gustavostuff/GameNerd/nano/apps/studio/app/src/ui/ui.h

#ifndef retr01_STUDIO_UI_H
#define retr01_STUDIO_UI_H

#include "retr01_studio/project.h"
#include "retr01_nano_emu/machine.h"
#include "r01_bgm_host.h"

#include <SDL.h>

#define UI_LOGIC_BASE_W 640
#define UI_LOGIC_BASE_H 360

/* Phase 2 chrome: dark / darker gray, 8px grid. */
#define UI_COL_BG_R 34
#define UI_COL_BG_G 34
#define UI_COL_BG_B 38
#define UI_COL_PANEL_R 26
#define UI_COL_PANEL_G 26
#define UI_COL_PANEL_B 30
#define UI_COL_WELL_R 63
#define UI_COL_WELL_G 63
#define UI_COL_WELL_B 74
#define UI_COL_ACTIVE_R 45
#define UI_COL_ACTIVE_G 125
#define UI_COL_ACTIVE_B 70
#define UI_COL_PRESENT_R 55
#define UI_COL_PRESENT_G 130
#define UI_COL_PRESENT_B 220
#define UI_COL_MARK_R 245
#define UI_COL_MARK_G 245
#define UI_COL_MARK_B 245
#define UI_COL_CHESS_A_R 58
#define UI_COL_CHESS_A_G 58
#define UI_COL_CHESS_A_B 66
#define UI_COL_CHESS_B_R 50
#define UI_COL_CHESS_B_G 50
#define UI_COL_CHESS_B_B 58

#define UI_UNIT 8
#define UI_BTN_H 16
#define UI_SIDEBAR_W 128
#define UI_CTRL_SIDEBAR_W 128
#define UI_WORLD_BTN 16
#define UI_WORLD_CELL 8 /* 16x16 map fits 128px sidebar */
#define UI_WORLD_VIEW 128
#define UI_PAL_SWATCH 8
#define UI_PAL_GRID_CELL 16 /* 4x4 picker cell (2x swatch) */
#define UI_PAL_GRID_SIZE (R01_PALS_PER_ROW * UI_PAL_GRID_CELL)
/* Nano FG picker: 2 rows × 4 colors (board FG 0..7). */
#define UI_FG_COLS 4
#define UI_FG_ROWS 2
#define UI_FG_CELL UI_PAL_GRID_CELL
#define UI_FG_GRID_W (UI_FG_COLS * UI_FG_CELL)
#define UI_FG_GRID_H (UI_FG_ROWS * UI_FG_CELL)

#define UI_WORLDS_X 0
#define UI_WORLDS_SUB_H 8
#define UI_TABS_TAB_H 8  /* active main tab height (16x16 inactive stack fill) */
#define UI_WORLDS_TAB_STACK_H 16 /* inactive dual-view tab fill / active main+sub */
#define UI_WORLDS_BODY_H (UI_BTN_H + UI_WORLD_VIEW)
#define UI_PAL_BODY_H (UI_PAL_SWATCH * 2 + UI_BTN_H)

#define UI_WORLDS_PLANE_BG1 0
#define UI_WORLDS_PLANE_BG0 1

#define UI_BANKS_PLANE_BG 0
#define UI_BANKS_N 4
#define UI_BANKS_GRID 128 /* 16x16 tiles @ 8px */
#define UI_BANKS_BODY_H (UI_BTN_H + UI_BANKS_GRID)

#define UI_ARM_NONE 0
#define UI_ARM_WORLD_TAB 1
#define UI_ARM_WORLD_SUB 2
#define UI_ARM_WORLD_CELL 3
#define UI_ARM_ACCORDION 4
#define UI_ARM_LAYER 5
#define UI_ARM_MODE 6
#define UI_ARM_PAL_STRIP 7
#define UI_ARM_PAL_ROW 8
#define UI_ARM_PLAY 9
#define UI_ARM_CATALOG_ADD 10
#define UI_ARM_BANK_TAB 12
#define UI_ARM_BANK_SUB 13
#define UI_ARM_APP_TAB 14
#define UI_ARM_SOUND_PLANE 15
#define UI_ARM_SOUND_TRACK 16
#define UI_ARM_SOUND_ADD 17
#define UI_ARM_SOUND_CH 18
#define UI_ARM_SOUND_PLAY 19
#define UI_ARM_SOUND_PAUSE 20
#define UI_ARM_SOUND_STOP 21

#define UI_APP_GRAPHICS 0
#define UI_APP_SOUNDS 1 /* Audio tab (historical enum name) */
#define UI_APP_CHROME_H UI_BTN_H /* Graphics|Audio strip, flush to content */

#define UI_SOUND_PLANE_BGM 0
#define UI_SOUND_PLANE_SFX 1
#define UI_SOUND_BGM_CH 1 /* Nano: single Music (Pulse) lane */
#define UI_SOUND_SOLO_ALL (-1) /* isolate radios: hear all channels */
#define UI_SOUND_SNAP_DIV R01_BGM_NOTE_DIV
#define UI_SOUND_STEPS_MAX R01_BGM_STEPS
#define UI_SOUND_TRACKS_MAX 8
#define UI_SOUND_REGIONS_MAX 128
#define UI_SOUND_CLIP_MAX 32
#define UI_SOUND_PX_PER_TICK 16 /* one 1/4-note tick = 2 grid cells */
#define UI_SOUND_LANE_H 16      /* channel strip height (2 grid cells) */
#define UI_SOUND_LANE_GAP 0
#define UI_SOUND_HANDLE_W 8
#define UI_SOUND_MINIMAP_H 8
#define UI_SOUND_SCROLL_PAD 4 /* unused for max; kept for content padding hints */

#define UI_SOUND_SEL_NONE 0
#define UI_SOUND_SEL_REGION 1
#define UI_SOUND_SEL_EMPTY 2

#define UI_SOUND_DRAG_NONE 0
#define UI_SOUND_DRAG_PAINT 1
#define UI_SOUND_DRAG_RESIZE_L 2
#define UI_SOUND_DRAG_RESIZE_R 3
#define UI_SOUND_DRAG_MOVE 4

#define UI_ACC_NONE (-1)
#define UI_ACC_WORLDS 0
#define UI_ACC_BANKS 1
#define UI_ACC_METATILES 2
/* When 1, all accordion sections stay expanded and headers do not collapse. */
#define UI_ACCORDION_ALWAYS_EXPANDED 0
#define UI_ACCORDION_ANIM_MS 250
#define UI_ACC_SECTIONS 3

#define UI_METATILES_BODY_H 96
#define UI_SPRITE_ROW_H 16
#define UI_PREVIEW_ICON 16

#define UI_DOT_SIZE 8
#define UI_DOT_GAP 0 /* packed strip, no gaps between dots */
#define UI_DOT_STRIP_N 4

/* Widget focus: wheel / keyboard route to the focused control. */
#define UI_FOCUS_NONE 0
#define UI_FOCUS_PALETTE 1
#define UI_FOCUS_WORKBENCH 2
#define UI_FOCUS_LIST 3

#define UI_MODE_ROW_H UI_BTN_H
#define UI_MODE_RADIO 8
#define UI_MODE_GAP 8
#define UI_CHECKBOX 8

#define UI_SCREEN_MODE_SEL 0
#define UI_SCREEN_MODE_PAINT 1

#define UI_SCREEN_LAYER_BG 0

#define UI_MODAL_W 288
#define UI_MODAL_H 184
#define UI_TILE_CANVAS 128
#define UI_MODAL_BODY_Y (UI_BTN_H + UI_UNIT)

#define UI_PAL_MODAL_W 320
#define UI_PAL_MODAL_H 192
#define UI_MASTER_COLS 16
#define UI_MASTER_ROWS 4
#define UI_MASTER_CELL 8
#define UI_PAL_EDIT_CELL UI_PAL_GRID_CELL

#define UI_TOAST_MS 2800
#define UI_TOOLTIP_DELAY_MS 400

#define UI_MENU_MAX 16
#define UI_MENU_KIND_TILE 1
#define UI_MENU_KIND_WORLD 2
#define UI_MENU_KIND_BANK_CELL 7
#define UI_MENU_KIND_METATILE 8
#define UI_MENU_SUB_NONE 0
#define UI_MENU_SUB_BANK 1
#define UI_MENU_SUB_PAL 2
#define UI_MENU_SUB_MOVE_BANK 6

typedef struct UiMenu {
    int open;
    int kind;
    int root_x, root_y;
    int root_w;
    int item_count;
    char items[UI_MENU_MAX][32];
    uint8_t item_sub[UI_MENU_MAX]; /* UI_MENU_SUB_* or 0 */
    uint8_t item_disabled[UI_MENU_MAX];

    int submenu;
    int sub_x, sub_y;
    int sub_w;
    int sub_count;
    char sub_items[UI_MENU_MAX][24];

    int screen_tx, screen_ty;
    int world_screen_idx;
    int metatile_idx;
    int bank_idx;     /* UI_MENU_KIND_BANK_CELL */
    int bank_tile_id;
    int bank_plane; /* UI_BANKS_PLANE_* */
} UiMenu;

typedef struct UiTileEdit {
    int open;
    int pal;   /* Nano FG color 0..7 */
    int color; /* paint ink 0/1 (1bpp) */
    int tile_id;
    int bank;
    int flip_h;
    int flip_v;
    int is_new;
    int edit_all; /* Shift: apply save to all matching tile+attr cells in world */
    uint8_t match_tile_id;
    uint8_t match_attr_hw; /* bank/pal/flips at open (R01_ATTR_HW_MASK) */
    uint8_t chr[R01_TILE_BYTES];
    int paint_tx, paint_ty; /* screen tile that opened the editor (-1 if none) */
} UiTileEdit;

typedef struct UiPalEdit {
    int open;
    int row;   /* 0..7 global palette row (BG + SPR) */
    int plane; /* 0 = BG, 1 = SPR */
    int pal;   /* 0..3 */
    int color; /* 0..3 */
    int snap_valid;
    int snap_default_row;
    R01PalRow snap_bg[R01_PAL_ROWS][R01_PALS_PER_ROW];
    R01PalRow snap_spr[R01_PAL_ROWS][R01_PALS_PER_ROW];
} UiPalEdit;

typedef struct UiBrush {
    int armed; /* after Save in tile editor */
    int bank;
    int tile_id;
    int pal; /* Nano: FG color 0..7 (attr bits) */
    int flip_h;
    int flip_v;
    uint8_t chr[R01_TILE_BYTES];
} UiBrush;

/* Painted note strip on a channel lane (UI source of truth; flattened for host). */
typedef struct UiBgmRegion {
    int start;   /* ticks */
    int len;     /* ticks, >= 1 */
    int midi;    /* melodic MIDI; noise period 0..15; DPCM kind stub */
    char tok[5]; /* host token */
} UiBgmRegion;

/* UI BGM shell (persisted in project.bgm). */
typedef struct UiSoundEdit {
    int plane; /* UI_SOUND_PLANE_BGM or SFX */
    int track_idx;
    int track_count;
    char track_name[UI_SOUND_TRACKS_MAX][24];
    int solo_ch; /* UI_SOUND_SOLO_ALL, or 0..UI_SOUND_BGM_CH-1 to isolate */
    int scroll_x; /* first visible tick */
    int sel_kind; /* UI_SOUND_SEL_* */
    int sel_ch;
    int sel_region; /* index when SEL_REGION */
    int sel_tick;   /* empty pivot tick when SEL_EMPTY */
    int playing;    /* host advancing */
    int paused;     /* halted but playhead retained */
    float play_pos; /* fractional tick; -1 idle */
    int drag;       /* UI_SOUND_DRAG_* */
    int drag_ch;
    int drag_region;
    int drag_origin;
    int drag_start0;
    int drag_len0;
    int drag_mx0; /* mouse x at paint/resize down (click vs drag) */
    int clip_valid;
    int clip_ch;
    int clip_count;
    UiBgmRegion clip[UI_SOUND_CLIP_MAX];
    int region_count[UI_SOUND_TRACKS_MAX][UI_SOUND_BGM_CH];
    UiBgmRegion region[UI_SOUND_TRACKS_MAX][UI_SOUND_BGM_CH][UI_SOUND_REGIONS_MAX];
} UiSoundEdit;

/* Single active text field (web-like caret / selection / scroll). */
typedef struct UiTextEdit {
    char *buf;
    int cap;
    int field_id; /* 0 = none; modal-specific otherwise */
    int caret;
    int anchor; /* selection other end; equals caret when collapsed */
    int scroll; /* horizontal px */
    int drag;   /* mouse-drag selecting */
} UiTextEdit;

/* Embedded emu Play session (export then cart-backed MAP preview). */
typedef struct UiPlaySession {
    int active;  /* playing or booting (blocks editor) */
    int booting; /* export + machine init pending after first boot frame */
    int spin;
    Uint32 last_tick;
    R01neMachine *machine;
    SDL_Texture *fb_tex;
    char err[256];
} UiPlaySession;

typedef struct UiState {
    R01Project *project;
    UiPlaySession play;
    char project_path[R01_PATH_MAX];
    char toast[96];
    Uint32 toast_until;
    int toast_error;
    char tooltip[160];
    int tooltip_x;
    int tooltip_y;
    int tooltip_arm_x; /* hover arm point; any move clears + resets delay */
    int tooltip_arm_y;
    int tooltip_active;
    int tooltip_hit; /* armed this frame via ui_tooltip_hover */
    Uint32 tooltip_since_ms;
    char tooltip_key[160];
    int scale;
    int logic_scale; /* 1 = 640x360, 2 = 1280x720 */
    Uint8 keys[512];
    int mouse_x;
    int mouse_y;
    UiMenu menu;
    UiTileEdit tile_edit;
    UiPalEdit pal_edit;
    UiTextEdit text;
    UiBrush brush;
    UiSoundEdit sound;
    int app_mode; /* UI_APP_GRAPHICS or UI_APP_SOUNDS */
    int paint_stamp_valid;
    uint8_t paint_stamp_tile;
    uint8_t paint_stamp_attr;
    int screen_mode;  /* UI_SCREEN_MODE_SEL or UI_SCREEN_MODE_PAINT */
    int screen_layer; /* UI_SCREEN_LAYER_BG */
    int sel_x0, sel_y0, sel_x1, sel_y1; /* inclusive tile rect; invalid when sel_x0 < 0 */
    int sel_anchor_x, sel_anchor_y;
    int sel_drag;
    int last_paint_tx;
    int last_paint_ty;
    Uint32 last_click_ms;
    int last_click_col;
    int last_click_row;
    int worlds_plane; /* UI_WORLDS_PLANE_BG1 or BG0 */
    int banks_idx;    /* 0..3 CHR bank tab */
    int banks_plane;  /* UI_BANKS_PLANE_BG */
    int world_sel_col; /* grid selection (-1 none); empty slots allowed */
    int world_sel_row;
    int screen_clip_valid;
    R01Screen screen_clip; /* Ctrl+C / Ctrl+V whole-screen buffer */
    int arm_kind;     /* UI_ARM_* chrome press-arm for release commit */
    int arm_a;
    int arm_b;
    int accordion_open; /* UI_ACC_* or UI_ACC_NONE */
    int accordion_body_h[UI_ACC_SECTIONS]; /* animated body height per section */
    Uint32 accordion_anim_last_ms;
    int metatiles_scroll;
    int focus; /* UI_FOCUS_* — which control owns wheel / key routing */
} UiState;

static inline int ui_logic_scale(const UiState *ui) {
    int s = ui ? ui->logic_scale : 2;
    return (s == 1) ? 1 : 2;
}

static inline int ui_logic_w(const UiState *ui) {
    return UI_LOGIC_BASE_W * ui_logic_scale(ui);
}

static inline int ui_logic_h(const UiState *ui) {
    return UI_LOGIC_BASE_H * ui_logic_scale(ui);
}

static inline int ui_main_w(const UiState *ui) {
    return ui_logic_w(ui) - UI_SIDEBAR_W - UI_CTRL_SIDEBAR_W;
}

static inline int ui_ctrl_x(const UiState *ui) {
    return ui_logic_w(ui) - UI_CTRL_SIDEBAR_W;
}

/*
 * Integer pixel scale for the 128×96 compose buffer in the main pane.
 * Largest fit between the sidebars, minus one (breathing room).
 */
static inline int ui_screen_scale(const UiState *ui) {
    int avail_w = ui_main_w(ui);
    int avail_h = ui_logic_h(ui) - UI_APP_CHROME_H - 2 * UI_UNIT;
    int max_sx;
    int max_sy;
    int s;
    (void)ui;
    if (avail_w < 1) {
        avail_w = 1;
    }
    if (avail_h < 1) {
        avail_h = 1;
    }
    max_sx = avail_w / R01_SCREEN_PX_W;
    max_sy = avail_h / R01_SCREEN_PX_H;
    s = max_sx < max_sy ? max_sx : max_sy;
    if (s > 1) {
        s -= 1;
    }
    if (s < 1) {
        s = 1;
    }
    return s;
}

static inline int ui_screen_w(const UiState *ui) {
    return R01_SCREEN_PX_W * ui_screen_scale(ui);
}

static inline int ui_screen_h(const UiState *ui) {
    return R01_SCREEN_PX_H * ui_screen_scale(ui);
}

static inline int ui_preview_x(const UiState *ui) {
    int pane = ui_main_w(ui);
    int sw = ui_screen_w(ui);
    int x = UI_SIDEBAR_W + (pane - sw) / 2;
    if (x < UI_SIDEBAR_W) {
        x = UI_SIDEBAR_W;
    }
    if (x + sw > ui_ctrl_x(ui)) {
        x = ui_ctrl_x(ui) - sw;
        if (x < UI_SIDEBAR_W) {
            x = UI_SIDEBAR_W;
        }
    }
    return x;
}

int ui_init(UiState *ui);
void ui_shutdown(UiState *ui);
void ui_tick(UiState *ui);
void ui_draw(UiState *ui, SDL_Renderer *r);
void ui_toggle_logic_scale(UiState *ui);
int ui_handle_event(UiState *ui, const SDL_Event *e, int lx, int ly);
int ui_handle_drop_file(UiState *ui, const char *path, int lx, int ly);

#endif
