gustavostuff/GameNerd/nano/apps/studio/app/src/ui/internal.h

#ifndef retr01_STUDIO_UI_INTERNAL_H
#define retr01_STUDIO_UI_INTERNAL_H

#include "ui/ui.h"
#include "ui/widgets/widgets.h"

#include <SDL.h>
#include <stdint.h>

typedef struct UiClipStack {
    SDL_Rect prev;
    SDL_bool had_clip;
} UiClipStack;

typedef struct AccordionLayout {
    int worlds_hdr_y;
    int worlds_btns_y;
    int worlds_grid_y;
    int worlds_open;
    int worlds_body_h;
    int banks_hdr_y;
    int banks_body_y;
    int banks_open;
    int banks_body_h;
    int metatiles_hdr_y;
    int metatiles_body_y;
    int metatiles_open;
    int metatiles_body_h;
} AccordionLayout;

typedef struct SoundEditorLayout {
    int content_y;
    int plane_tabs_x, plane_tabs_y, plane_tab_w;
    int track_list_y, track_row_h;
    int add_x, add_y, add_w;
    int hdr_y;
    int lane_label_x, lane_label_w;
    int timeline_x, timeline_y, timeline_w, timeline_h;
    int lane_h, lane_gap;
    int px_per_tick;
    int visible_ticks;
    int ruler_h;
    int minimap_y, minimap_h;
    int insp_x, insp_y;
    int play_x, play_y, play_w;
    int pause_x, pause_y, pause_w;
    int stop_x, stop_y, stop_w;
    int ch_radio_y0;
} SoundEditorLayout;

static inline void ui_world_btn_pos(int wi, int btns_y, int *out_x, int *out_y) {
    if (out_x) {
        *out_x = UI_WORLDS_X + wi * UI_WORLD_BTN;
    }
    if (out_y) {
        *out_y = btns_y;
    }
}

typedef struct TileModalLayout {
    int mx, my;
    int pal_x, pal_label_y, pal_y;
    int canvas_x, canvas_y;
    int btn_y, save_w, cancel_w;
} TileModalLayout;

typedef struct PalModalLayout {
    int mx, my;
    int master_x, master_y;
    int bg_label_y, bg_x, bg_y;
    int spr_label_y, spr_x, spr_y;
    int btn_y, save_w, cancel_w;
} PalModalLayout;

extern uint8_t *g_radio_rgba;
extern int g_radio_w;
extern int g_radio_h;
extern uint8_t *g_dot_rgba;
extern int g_dot_w;
extern int g_dot_h;
extern uint8_t *g_checkbox_rgba;
extern int g_checkbox_w;
extern int g_checkbox_h;
extern uint8_t *g_cross_rgba;
extern int g_cross_w;
extern int g_cross_h;
extern uint8_t *g_bg0_btn_rgba;
extern int g_bg0_btn_w;
extern int g_bg0_btn_h;
extern uint8_t *g_bg1_btn_rgba;
extern int g_bg1_btn_w;
extern int g_bg1_btn_h;
extern uint8_t *g_bg_bank_btn_rgba;
extern int g_bg_bank_btn_w;
extern int g_bg_bank_btn_h;
extern uint8_t *g_spr_bank_btn_rgba;
extern int g_spr_bank_btn_w;
extern int g_spr_bank_btn_h;

extern SDL_Cursor *g_cursor_arrow;
extern SDL_Cursor *g_cursor_hand;
extern SDL_Cursor *g_cursor_sizewe;

int ui_load_png_rgba(const char *path, uint8_t **out_px, int *out_w, int *out_h);
int ui_paste_clipboard_png_tile(UiState *ui, uint8_t chr[R01_TILE_BYTES], int pal, int spr_plane);
int snap8(int v);
void ui_toast(UiState *ui, const char *msg, int is_error);
void ui_tooltip_set(UiState *ui, int x, int y, const char *line1, const char *line2);
void ui_tooltip_hover(UiState *ui, int x, int y, const char *line1, const char *line2);
void ui_tooltip_frame_begin(UiState *ui);
void ui_tooltip_frame_end(UiState *ui);
void ui_tooltip_clear(UiState *ui);
void draw_tooltip(UiState *ui, SDL_Renderer *r);
void ui_focus_set(UiState *ui, int focus);
int ui_focus_get(const UiState *ui);
void ui_focus_clear(UiState *ui);
void fill_rect(SDL_Renderer *r, int x, int y, int w, int h, Uint8 R, Uint8 G, Uint8 B);
void fill_rect_alpha(SDL_Renderer *r, int x, int y, int w, int h, Uint8 R, Uint8 G, Uint8 B, Uint8 A);
void ui_clip_push(SDL_Renderer *r, int x, int y, int w, int h, UiClipStack *stack);
void ui_clip_pop(SDL_Renderer *r, const UiClipStack *stack);
void draw_rect(SDL_Renderer *r, int x, int y, int w, int h, Uint8 R, Uint8 G, Uint8 B);
void hover_overlay(SDL_Renderer *r, int x, int y, int w, int h);
void font_draw_clipped(SDL_Renderer *r, int x, int y, int clip_x, int clip_y, int clip_w, int clip_h,
                       const char *text, Uint8 R, Uint8 G, Uint8 B);
int point_in_rect(int lx, int ly, int x, int y, int w, int h);
int label_width(const char *text);
void draw_brush_preview(SDL_Renderer *r, const R01Project *p, int row, int pal, int color, int mx, int my);
void draw_ui_cross(SDL_Renderer *r, int cx, int cy);
void draw_label(SDL_Renderer *r, int x, int y, const char *text);
void draw_chess_grid(SDL_Renderer *r, int x0, int y0, int cols, int rows, int cell);

void ui_editor_layout(const UiState *ui, int *screen_x, int *screen_y, int *layer_x, int *mode_x, int *mode_y0);
void ui_preview_size(const UiState *ui, int *out_w, int *out_h);
int screen_mode_hit(const UiState *ui, int lx, int ly, int *out_row);
int screen_mode_row_hit(const UiState *ui, int lx, int ly, int row);
int screen_layer_hit(const UiState *ui, int lx, int ly, int *out_layer);
int screen_layer_row_hit(const UiState *ui, int lx, int ly, int row);
int ui_mode_label_x(int mode_x);
int ui_mode_panel_w(void);
int ui_layer_panel_w(void);
void screen_origin(const UiState *ui, int *ox, int *oy);
int screen_hit(const UiState *ui, int lx, int ly, int *out_tx, int *out_ty);
int screen_pixel_hit(const UiState *ui, int lx, int ly, int *out_px, int *out_py);
void accordion_init_heights(UiState *ui);
void accordion_anim_tick(UiState *ui);
void accordion_layout(const UiState *ui, AccordionLayout *lo);
int world_cell_hit(const UiState *ui, int lx, int ly, int *out_col, int *out_row);
int world_btn_hit(const UiState *ui, int lx, int ly, int *out_wi);
int world_sub_hit(const UiState *ui, int lx, int ly);
void worlds_tabs_prepare(const UiState *ui, UiTabsLayout *out);
int accordion_header_hit(const UiState *ui, int lx, int ly, int *out_section);
void accordion_toggle(UiState *ui, int section);
void draw_accordion_header(SDL_Renderer *r, int y, const char *title, int open, int hover);
void app_mode_tabs_prepare(const UiState *ui, UiTabsLayout *out);
int app_mode_tab_hit(const UiState *ui, int lx, int ly, int *out_idx);
void draw_app_mode_tabs(UiState *ui, SDL_Renderer *r);
void sound_editor_layout(const UiState *ui, SoundEditorLayout *lo);
void sound_plane_tabs_prepare(const UiState *ui, UiTabsLayout *out);
int sound_plane_tab_hit(const UiState *ui, int lx, int ly, int *out_idx);
int sound_track_hit(const UiState *ui, int lx, int ly, int *out_idx);
int sound_add_hit(const UiState *ui, int lx, int ly);
int sound_timeline_hit(const UiState *ui, int lx, int ly, int *out_ch, int *out_tick);
int sound_region_hit(const UiState *ui, int lx, int ly, int *out_ch, int *out_region, int *out_handle);
int sound_channel_hit(const UiState *ui, int lx, int ly, int *out_ch);
int sound_play_hit(const UiState *ui, int lx, int ly);
int sound_pause_hit(const UiState *ui, int lx, int ly);
int sound_stop_hit(const UiState *ui, int lx, int ly);
void ui_sound_init(UiState *ui);
int ui_sound_audio_init(void);
void ui_sound_audio_shutdown(void);
void ui_sound_play_start(UiState *ui);
void ui_sound_play_stop(UiState *ui);
void ui_sound_play_pause(UiState *ui);
void ui_sound_play_toggle(UiState *ui);
void ui_sound_play_poll(UiState *ui);
int ui_sound_play_step(void);
void tile_modal_layout(const UiState *ui, TileModalLayout *lo);
void pal_modal_layout(const UiState *ui, PalModalLayout *lo);
int play_btn_w(const UiState *ui);
int play_btn_x(const UiState *ui);
int play_btn_y(const UiState *ui);
int play_button_hit(const UiState *ui, int lx, int ly);
int banks_cell_hit(const UiState *ui, int lx, int ly, int *out_tile_id);
int banks_tab_hit(const UiState *ui, int lx, int ly, int *out_idx);
int banks_sub_hit(const UiState *ui, int lx, int ly);
void banks_tabs_prepare(const UiState *ui, UiTabsLayout *out);
int metatiles_list_hit(const UiState *ui, int lx, int ly, int *out_idx);
int metatiles_add_hit(const UiState *ui, int lx, int ly);

int palette_strip_hit(const UiState *ui, int lx, int ly);
int palette_row_btn_hit(const UiState *ui, int lx, int ly, int *out_row);
void pal_edit_close(UiState *ui);
void pal_edit_cancel(UiState *ui);
void pal_edit_save(UiState *ui);
void pal_edit_open(UiState *ui);
void pal_edit_set_row(UiState *ui, int row, int commit_default);
void pal_edit_nudge_master(UiState *ui, int wheel_y, int shift);
int pal_modal_master_hit(const UiState *ui, int lx, int ly, int *out_col, int *out_row);
int pal_modal_plane_hit(const UiState *ui, int lx, int ly, int plane, int *out_pal, int *out_color);
int pal_modal_handle(UiState *ui, int lx, int ly, int down);
void draw_pal_modal(UiState *ui, SDL_Renderer *r);

void menu_close(UiState *ui);
void menu_sync_tile_edit_label(UiState *ui);
void menu_open_tile(UiState *ui, int x, int y, int tx, int ty);
void menu_open_world_cell(UiState *ui, int x, int y, int screen_idx);
void menu_open_bank_cell(UiState *ui, int x, int y, int bank, int tile_id, int plane);
void menu_open_metatile(UiState *ui, int x, int y, int metatile_idx);
int menu_hit(const UiState *ui, int lx, int ly, int *out_item, int *out_sub);
void menu_update_hover(UiState *ui, int lx, int ly);
void handle_menu_pick(UiState *ui, int item, int is_sub);

void screen_sel_set(UiState *ui, int x0, int y0, int x1, int y1);
void screen_sel_clear(UiState *ui);
int screen_sel_valid(const UiState *ui);
void screen_sel_bounds(const UiState *ui, int *min_x, int *min_y, int *max_x, int *max_y);
void screen_refresh_sel(UiState *ui);
int screen_sel_is_multi(const UiState *ui);

void ui_paint_stamp_set(UiState *ui, uint8_t tile, uint8_t attr);
void ui_paint_stamp_from_bank(UiState *ui, int bank, int tile_id);
void ui_paint_stamp_from_cell(UiState *ui, int tx, int ty);
int ui_paint_stamp_from_sel(const UiState *ui, uint8_t *out_tile, uint8_t *out_attr);
void ui_paint_tile(UiState *ui, int tx, int ty);
void ui_flood_fill(UiState *ui, int tx, int ty);

void ui_toggle_play(UiState *ui);
void ui_play_stop(UiState *ui);
void ui_play_boot_finish(UiState *ui, SDL_Renderer *ren);
int ui_play_screen_mark(const UiState *ui);
void screen_set_sel_bank(UiState *ui, int bank);
void screen_set_sel_pal(UiState *ui, int pal);
void screen_toggle_sel_flag(UiState *ui, uint8_t flag);
void screen_set_solid_by_hw(UiState *ui, int ref_tx, int ref_ty);

void draw_screen_editor(UiState *ui, SDL_Renderer *r, const R01Screen *s);
void draw_play_view(UiState *ui, SDL_Renderer *r);
void draw_catalog_drag_ghost(UiState *ui, SDL_Renderer *r);

void tile_edit_open(UiState *ui, int tx, int ty);
void tile_edit_open_all(UiState *ui, int tx, int ty);
void tile_edit_open_new(UiState *ui, int tx, int ty);
void tile_edit_open_bank(UiState *ui, int bank, int tile_id, int is_new);
int tile_modal_handle(UiState *ui, int lx, int ly, int down, Uint8 button);
void draw_tile_modal(UiState *ui, SDL_Renderer *r);

void ui_update_cursor(const UiState *ui);
void draw_screen_mode(UiState *ui, SDL_Renderer *r);
void draw_ctrl_sidebar(UiState *ui, SDL_Renderer *r);
void draw_sound_editor(UiState *ui, SDL_Renderer *r);
void draw_sidebar(UiState *ui, SDL_Renderer *r);
void draw_menu(UiState *ui, SDL_Renderer *r);

void ui_reset_after_project_load(UiState *ui);
void ui_save(UiState *ui);
void ui_export(UiState *ui);

int ui_screen_nav(UiState *ui, int dcol, int drow);
R01Screen *ui_edit_map_screen(const UiState *ui);
void handle_world_click(UiState *ui, int col, int row, int ctrl, int dbl);
int ui_world_screen_copy(UiState *ui);
int ui_world_screen_paste(UiState *ui);
int ui_world_screen_remove(UiState *ui);

#endif
