gustavostuff/GameNerd/nano/apps/studio/app/src/ui/layout.c

#include "ui/ui.h"
#include "ui/internal.h"
#include "ui/sound/bgm_edit.h"
#include "font/font.h"

#include "retr01_studio/cart.h"
#include "retr01_studio/chr_pack.h"
#include "retr01_studio/json_io.h"
#include "retr01_studio/palette.h"
#include "retr01_studio/project.h"

#include <png.h>
#include <stdio.h>
#include <stdlib.h>
#include <string.h>

int ui_mode_panel_w(void) {
    int label_x = UI_MODE_RADIO + UI_MODE_GAP;
    int w0 = label_x + label_width("Tile selection");
    int w1 = label_x + label_width("Tile paint");
    int w = w0;
    if (w1 > w) {
        w = w1;
    }
    return w;
}

int ui_layer_panel_w(void) {
    return ui_mode_panel_w();
}

void ui_preview_size(const UiState *ui, int *out_w, int *out_h) {
    if (out_w) {
        *out_w = ui_screen_w(ui);
    }
    if (out_h) {
        *out_h = ui_screen_h(ui);
    }
}

void ui_editor_layout(const UiState *ui, int *screen_x, int *screen_y, int *layer_x, int *mode_x, int *mode_y0) {
    int sx = ui_preview_x(ui);
    int sy;
    int sh = ui_screen_h(ui);
    int chrome = UI_APP_CHROME_H;
    int content_h;
    int ctrl_inner = ui_ctrl_x(ui) + UI_UNIT;
    int radios_y = chrome + UI_BTN_H + UI_UNIT;
    int y_max;

    content_h = ui_logic_h(ui) - chrome;
    sy = chrome + (content_h - sh) / 2;
    if (sy < chrome + UI_UNIT) {
        sy = chrome + UI_UNIT;
    }
    y_max = ui_logic_h(ui) - UI_UNIT - sh;
    if (y_max < chrome + UI_UNIT) {
        y_max = chrome + UI_UNIT;
    }
    if (sy > y_max) {
        sy = y_max;
    }
    if (screen_x) {
        *screen_x = sx;
    }
    if (screen_y) {
        *screen_y = sy;
    }
    if (layer_x) {
        *layer_x = ctrl_inner;
    }
    if (mode_x) {
        *mode_x = ctrl_inner;
    }
    if (mode_y0) {
        *mode_y0 = radios_y;
    }
}

int ui_mode_label_x(int mode_x) {
    return mode_x + UI_MODE_RADIO + UI_MODE_GAP;
}

int screen_mode_row_hit(const UiState *ui, int lx, int ly, int row) {
    int sx, sy, layer_x, mx, my0;
    int y;
    if (!ui || ui->play.active) {
        return 0;
    }
    ui_editor_layout(ui, &sx, &sy, &layer_x, &mx, &my0);
    /* Mode radios: rows 0 and 1 (Tile selection / Tile paint). */
    y = my0 + row * UI_MODE_ROW_H;
    return point_in_rect(lx, ly, mx, y, ui_mode_panel_w(), UI_MODE_ROW_H);
}

int screen_mode_hit(const UiState *ui, int lx, int ly, int *out_row) {
    if (screen_mode_row_hit(ui, lx, ly, 0)) {
        if (out_row) {
            *out_row = UI_SCREEN_MODE_SEL;
        }
        return 1;
    }
    if (screen_mode_row_hit(ui, lx, ly, 1)) {
        if (out_row) {
            *out_row = UI_SCREEN_MODE_PAINT;
        }
        return 1;
    }
    return 0;
}

int screen_layer_row_hit(const UiState *ui, int lx, int ly, int row) {
    (void)ui;
    (void)lx;
    (void)ly;
    (void)row;
    return 0;
}

int screen_layer_hit(const UiState *ui, int lx, int ly, int *out_layer) {
    (void)ui;
    (void)lx;
    (void)ly;
    if (out_layer) {
        *out_layer = UI_SCREEN_LAYER_BG;
    }
    return 0;
}

int play_btn_w(const UiState *ui) {
    return label_width(ui->play.active ? "Stop" : "Play");
}

int play_btn_x(const UiState *ui) {
    int w = play_btn_w(ui);
    (void)ui;
    return ui_ctrl_x(ui) + (UI_CTRL_SIDEBAR_W - w) / 2;
}

int play_btn_y(const UiState *ui) {
    (void)ui;
    return UI_APP_CHROME_H;
}

int play_button_hit(const UiState *ui, int lx, int ly) {
    int x = play_btn_x(ui);
    int y = play_btn_y(ui);
    int w = play_btn_w(ui);
    return lx >= x && lx < x + w && ly >= y && ly < y + UI_BTN_H;
}

void screen_origin(const UiState *ui, int *ox, int *oy) {
    int sx, sy, layer_x, mx, my0;
    ui_editor_layout(ui, &sx, &sy, &layer_x, &mx, &my0);
    *ox = sx;
    *oy = sy;
}

int screen_hit(const UiState *ui, int lx, int ly, int *out_tx, int *out_ty) {
    int ox, oy;
    int lx0, ly0;
    screen_origin(ui, &ox, &oy);
    if (lx < ox || ly < oy || lx >= ox + ui_screen_w(ui) || ly >= oy + ui_screen_h(ui)) {
        return 0;
    }
    lx0 = (lx - ox) / ui_screen_scale(ui);
    ly0 = (ly - oy) / ui_screen_scale(ui);
    if (lx0 >= R01_SCREEN_PX_W || ly0 >= R01_SCREEN_PX_H) {
        return 0;
    }
    if (out_tx) {
        *out_tx = lx0 / 8;
    }
    if (out_ty) {
        *out_ty = ly0 / 8;
    }
    return 1;
}

int screen_pixel_hit(const UiState *ui, int lx, int ly, int *out_px, int *out_py) {
    int ox, oy;
    int px, py;
    screen_origin(ui, &ox, &oy);
    if (lx < ox || ly < oy || lx >= ox + ui_screen_w(ui) || ly >= oy + ui_screen_h(ui)) {
        return 0;
    }
    px = (lx - ox) / ui_screen_scale(ui);
    py = (ly - oy) / ui_screen_scale(ui);
    if (px < 0 || py < 0 || px >= R01_SCREEN_PX_W || py >= R01_SCREEN_PX_H) {
        return 0;
    }
    if (out_px) {
        *out_px = px;
    }
    if (out_py) {
        *out_py = py;
    }
    return 1;
}

void accordion_layout(const UiState *ui, AccordionLayout *lo) {
    int y = UI_APP_CHROME_H;
    int always = UI_ACCORDION_ALWAYS_EXPANDED;
    int worlds_h = 0;
    int banks_h = 0;
    int metatiles_h = 0;

    memset(lo, 0, sizeof(*lo));
    lo->metatiles_hdr_y = -1;
    lo->metatiles_body_y = -1;

    if (always) {
        worlds_h = UI_WORLDS_BODY_H;
        banks_h = UI_BANKS_BODY_H;
        metatiles_h = UI_METATILES_BODY_H;
    } else if (ui) {
        worlds_h = ui->accordion_body_h[UI_ACC_WORLDS];
        banks_h = ui->accordion_body_h[UI_ACC_BANKS];
        metatiles_h = ui->accordion_body_h[UI_ACC_METATILES];
    }

    lo->worlds_hdr_y = y;
    y += UI_BTN_H;
    lo->worlds_open = always || (ui && ui->accordion_open == UI_ACC_WORLDS);
    lo->worlds_body_h = worlds_h;
    if (worlds_h > 0) {
        lo->worlds_btns_y = y;
        lo->worlds_grid_y = y + UI_BTN_H;
        y += worlds_h;
    } else {
        lo->worlds_btns_y = -1;
        lo->worlds_grid_y = -1;
    }

    lo->banks_hdr_y = y;
    y += UI_BTN_H;
    lo->banks_open = always || (ui && ui->accordion_open == UI_ACC_BANKS);
    lo->banks_body_h = banks_h;
    if (banks_h > 0) {
        lo->banks_body_y = y;
        y += banks_h;
    } else {
        lo->banks_body_y = -1;
    }

    lo->metatiles_hdr_y = y;
    y += UI_BTN_H;
    lo->metatiles_open = always || (ui && ui->accordion_open == UI_ACC_METATILES);
    lo->metatiles_body_h = metatiles_h;
    if (metatiles_h > 0) {
        lo->metatiles_body_y = y;
        y += metatiles_h;
    } else {
        lo->metatiles_body_y = -1;
    }
}

static int accordion_section_full_h(int section) {
    switch (section) {
    case UI_ACC_WORLDS:
        return UI_WORLDS_BODY_H;
    case UI_ACC_BANKS:
        return UI_BANKS_BODY_H;
    case UI_ACC_METATILES:
        return UI_METATILES_BODY_H;
    default:
        return 0;
    }
}

void accordion_init_heights(UiState *ui) {
    int i;
    if (!ui) {
        return;
    }
    for (i = 0; i < UI_ACC_SECTIONS; i++) {
        int full = accordion_section_full_h(i);
        if (UI_ACCORDION_ALWAYS_EXPANDED || ui->accordion_open == i) {
            ui->accordion_body_h[i] = full;
        } else {
            ui->accordion_body_h[i] = 0;
        }
    }
    ui->accordion_anim_last_ms = SDL_GetTicks();
}

void accordion_anim_tick(UiState *ui) {
    Uint32 now;
    Uint32 dt;
    int i;

    if (!ui) {
        return;
    }
    now = SDL_GetTicks();
    dt = now - ui->accordion_anim_last_ms;
    ui->accordion_anim_last_ms = now;
    if (dt > 100u) {
        dt = 100u;
    }
    if (UI_ACCORDION_ALWAYS_EXPANDED) {
        for (i = 0; i < UI_ACC_SECTIONS; i++) {
            ui->accordion_body_h[i] = accordion_section_full_h(i);
        }
        return;
    }
    for (i = 0; i < UI_ACC_SECTIONS; i++) {
        int full = accordion_section_full_h(i);
        int target = (ui->accordion_open == i) ? full : 0;
        int cur = ui->accordion_body_h[i];
        int step;

        if (cur == target || full <= 0) {
            continue;
        }
        step = (int)((long long)full * (long long)dt / UI_ACCORDION_ANIM_MS);
        if (step < 1) {
            step = 1;
        }
        if (cur < target) {
            cur += step;
            if (cur > target) {
                cur = target;
            }
        } else {
            cur -= step;
            if (cur < target) {
                cur = target;
            }
        }
        ui->accordion_body_h[i] = cur;
    }
}
int world_cell_hit(const UiState *ui, int lx, int ly, int *out_col, int *out_row) {
    AccordionLayout lo;
    int x0 = UI_WORLDS_X;
    int y0;
    int col, row;
    accordion_layout(ui, &lo);
    if (lo.worlds_body_h < 1) {
        return 0;
    }
    y0 = lo.worlds_grid_y;
    if (lo.worlds_body_h <= UI_BTN_H || y0 < 0) {
        return 0;
    }
    if (lx < x0 || ly < y0 || lx >= x0 + R01_GRID_MAX * UI_WORLD_CELL ||
        ly >= y0 + R01_GRID_MAX * UI_WORLD_CELL) {
        return 0;
    }
    if (ly >= lo.worlds_btns_y + lo.worlds_body_h) {
        return 0;
    }
    col = (lx - x0) / UI_WORLD_CELL;
    row = (ly - y0) / UI_WORLD_CELL;
    if (col < 0 || row < 0 || col >= R01_GRID_MAX || row >= R01_GRID_MAX) {
        return 0;
    }
    if (out_col) {
        *out_col = col;
    }
    if (out_row) {
        *out_row = row;
    }
    return 1;
}

int world_btn_hit(const UiState *ui, int lx, int ly, int *out_wi) {
    AccordionLayout lo;
    UiTabsLayout tabs;
    int sel;
    accordion_layout(ui, &lo);
    if (lo.worlds_body_h < 1 || lo.worlds_btns_y < 0) {
        return 0;
    }
    worlds_tabs_prepare(ui, &tabs);
    sel = (ui && ui->project) ? ui->project->active_world : 0;
    return ui_tabs_hit(&tabs, sel, lx, ly, out_wi);
}

void worlds_tabs_prepare(const UiState *ui, UiTabsLayout *out) {
    AccordionLayout lo;
    static const char *const world_labs[R01_MAX_WORLDS] = {"", "", "", "", "", "", "", ""};
    if (!out) {
        return;
    }
    accordion_layout(ui, &lo);
    ui_tabs_layout(world_labs, R01_MAX_WORLDS, UI_WORLDS_X, lo.worlds_btns_y, UI_WORLD_BTN, out);
    ui_tabs_set_dot(out, 1);
}

void banks_tabs_prepare(const UiState *ui, UiTabsLayout *out) {
    AccordionLayout lo;
    static const char *const bank_labs[UI_BANKS_N] = {"", "", "", ""};
    if (!out) {
        return;
    }
    accordion_layout(ui, &lo);
    ui_tabs_layout(bank_labs, UI_BANKS_N, UI_WORLDS_X, lo.banks_body_y, UI_WORLD_BTN, out);
    ui_tabs_set_dot(out, 1);
}

int banks_tab_hit(const UiState *ui, int lx, int ly, int *out_idx) {
    UiTabsLayout tabs;
    AccordionLayout lo;
    int sel;
    if (!ui) {
        return 0;
    }
    accordion_layout(ui, &lo);
    if (lo.banks_body_h < 1) {
        return 0;
    }
    banks_tabs_prepare(ui, &tabs);
    sel = ui->banks_idx;
    if (sel < 0) {
        sel = 0;
    }
    if (sel >= UI_BANKS_N) {
        sel = UI_BANKS_N - 1;
    }
    return ui_tabs_hit(&tabs, sel, lx, ly, out_idx);
}

int banks_sub_hit(const UiState *ui, int lx, int ly) {
    (void)ui;
    (void)lx;
    (void)ly;
    return 0;
}

int banks_cell_hit(const UiState *ui, int lx, int ly, int *out_tile_id) {
    AccordionLayout lo;
    int grid_y;
    int tx, ty;
    if (!ui || ui->play.active) {
        return 0;
    }
    accordion_layout(ui, &lo);
    if (lo.banks_body_h < UI_BANKS_BODY_H) {
        return 0;
    }
    grid_y = lo.banks_body_y + UI_BTN_H;
    if (lx < UI_WORLDS_X || lx >= UI_WORLDS_X + UI_BANKS_GRID || ly < grid_y || ly >= grid_y + UI_BANKS_GRID) {
        return 0;
    }
    tx = (lx - UI_WORLDS_X) / 8;
    ty = (ly - grid_y) / 8;
    if (tx < 0 || tx >= 16 || ty < 0 || ty >= 16) {
        return 0;
    }
    if (out_tile_id) {
        *out_tile_id = ty * 16 + tx;
    }
    return 1;
}

int world_sub_hit(const UiState *ui, int lx, int ly) {
    (void)ui;
    (void)lx;
    (void)ly;
    return 0;
}

int accordion_header_hit(const UiState *ui, int lx, int ly, int *out_section) {
    AccordionLayout lo;
    if (UI_ACCORDION_ALWAYS_EXPANDED) {
        return 0;
    }
    if (lx < 0 || lx >= UI_SIDEBAR_W) {
        return 0;
    }
    accordion_layout(ui, &lo);
    if (ly >= lo.worlds_hdr_y && ly < lo.worlds_hdr_y + UI_BTN_H) {
        if (out_section) {
            *out_section = UI_ACC_WORLDS;
        }
        return 1;
    }
    if (ly >= lo.banks_hdr_y && ly < lo.banks_hdr_y + UI_BTN_H) {
        if (out_section) {
            *out_section = UI_ACC_BANKS;
        }
        return 1;
    }
    if (ly >= lo.metatiles_hdr_y && ly < lo.metatiles_hdr_y + UI_BTN_H) {
        if (out_section) {
            *out_section = UI_ACC_METATILES;
        }
        return 1;
    }
    return 0;
}

void accordion_toggle(UiState *ui, int section) {
    if (UI_ACCORDION_ALWAYS_EXPANDED) {
        return;
    }
    if (ui->accordion_open == section) {
        ui->accordion_open = UI_ACC_NONE;
    } else {
        ui->accordion_open = section;
    }
}

void draw_accordion_header(SDL_Renderer *r, int y, const char *title, int open, int hover) {
    if (open) {
        fill_rect(r, 0, y, UI_SIDEBAR_W, UI_BTN_H, UI_COL_WELL_R, UI_COL_WELL_G, UI_COL_WELL_B);
    } else {
        fill_rect(r, 0, y, UI_SIDEBAR_W, UI_BTN_H, UI_COL_PANEL_R, UI_COL_PANEL_G, UI_COL_PANEL_B);
    }
    font_draw_centered(r, 0, y, UI_SIDEBAR_W, UI_BTN_H, title, 230, 230, 230);
    if (hover && !UI_ACCORDION_ALWAYS_EXPANDED) {
        hover_overlay(r, 0, y, UI_SIDEBAR_W, UI_BTN_H);
    }
}
static int modal_x(const UiState *ui) {
    return (ui_logic_w(ui) - UI_MODAL_W) / 2;
}

static int modal_y(const UiState *ui) {
    return (ui_logic_h(ui) - UI_MODAL_H) / 2;
}

void tile_modal_layout(const UiState *ui, TileModalLayout *lo) {
    lo->mx = modal_x(ui);
    lo->my = modal_y(ui);
    lo->pal_x = lo->mx + UI_UNIT * 2;
    lo->pal_label_y = lo->my + UI_MODAL_BODY_Y;
    lo->pal_y = lo->pal_label_y + UI_BTN_H;
    lo->canvas_x = lo->mx + UI_MODAL_W - UI_UNIT - UI_TILE_CANVAS;
    lo->canvas_y = lo->my + UI_MODAL_BODY_Y;
    lo->btn_y = lo->my + UI_MODAL_H - UI_BTN_H - UI_UNIT;
    lo->save_w = label_width("Save");
    lo->cancel_w = label_width("Cancel");
}

static int pal_modal_x(const UiState *ui) {
    return (ui_logic_w(ui) - UI_PAL_MODAL_W) / 2;
}

static int pal_modal_y(const UiState *ui) {
    return (ui_logic_h(ui) - UI_PAL_MODAL_H) / 2;
}

void pal_modal_layout(const UiState *ui, PalModalLayout *lo) {
    lo->mx = pal_modal_x(ui);
    lo->my = pal_modal_y(ui);
    lo->master_x = lo->mx + UI_UNIT * 2;
    lo->master_y = lo->my + UI_MODAL_BODY_Y + UI_BTN_H;
    lo->bg_label_y = lo->master_y + UI_MASTER_ROWS * UI_MASTER_CELL + UI_UNIT;
    lo->bg_x = lo->master_x;
    lo->bg_y = lo->bg_label_y + UI_BTN_H;
    lo->spr_label_y = lo->bg_label_y;
    lo->spr_x = lo->bg_x + R01_PALS_PER_ROW * UI_PAL_EDIT_CELL + UI_UNIT * 2;
    lo->spr_y = lo->bg_y;
    lo->btn_y = lo->my + UI_PAL_MODAL_H - UI_BTN_H - UI_UNIT;
    lo->save_w = label_width("Save");
    lo->cancel_w = label_width("Cancel");
}





int metatiles_list_hit(const UiState *ui, int lx, int ly, int *out_idx) {
    AccordionLayout lo;
    const R01World *w;
    int row, idx;
    if (!ui || ui->play.active) {
        return 0;
    }
    accordion_layout(ui, &lo);
    if (lo.metatiles_body_h < 1) {
        return 0;
    }
    w = r01_project_active_world_const(ui->project);
    if (!w || w->metatile_count < 1) {
        return 0;
    }
    if (lx < UI_WORLDS_X || lx >= UI_SIDEBAR_W || ly < lo.metatiles_body_y ||
        ly >= lo.metatiles_body_y + lo.metatiles_body_h) {
        return 0;
    }
    row = (ly - lo.metatiles_body_y) / UI_SPRITE_ROW_H;
    idx = ui->metatiles_scroll + row;
    if (idx < 0 || idx >= w->metatile_count) {
        return 0;
    }
    if (out_idx) {
        *out_idx = idx;
    }
    return 1;
}

int metatiles_add_hit(const UiState *ui, int lx, int ly) {
    AccordionLayout lo;
    int add_y;
    int add_w;
    if (!ui || ui->play.active) {
        return 0;
    }
    accordion_layout(ui, &lo);
    if (lo.metatiles_body_h < UI_BTN_H) {
        return 0;
    }
    add_y = lo.metatiles_body_y + UI_METATILES_BODY_H - UI_BTN_H;
    add_w = label_width("Add");
    return point_in_rect(lx, ly, UI_WORLDS_X + UI_UNIT, add_y, add_w, UI_BTN_H) &&
           ly < lo.metatiles_body_y + lo.metatiles_body_h;
}






void app_mode_tabs_prepare(const UiState *ui, UiTabsLayout *out) {
    static const char *const labs[] = {"Graphics", "Audio"};
    int tab_w;
    (void)ui;
    if (!out) {
        return;
    }
    tab_w = label_width("Graphics");
    if (label_width("Audio") > tab_w) {
        tab_w = label_width("Audio");
    }
    tab_w += UI_UNIT * 2;
    if (tab_w < 64) {
        tab_w = 64;
    }
    ui_tabs_layout(labs, 2, 0, 0, tab_w, out);
    out->tab_h = UI_BTN_H;
}

int app_mode_tab_hit(const UiState *ui, int lx, int ly, int *out_idx) {
    UiTabsLayout tabs;
    app_mode_tabs_prepare(ui, &tabs);
    return ui_tabs_hit(&tabs, ui ? ui->app_mode : 0, lx, ly, out_idx);
}

void draw_app_mode_tabs(UiState *ui, SDL_Renderer *r) {
    UiTabsLayout tabs;
    if (!ui || !r) {
        return;
    }
    fill_rect(r, 0, 0, ui_logic_w(ui), UI_APP_CHROME_H, UI_COL_PANEL_R, UI_COL_PANEL_G, UI_COL_PANEL_B);
    app_mode_tabs_prepare(ui, &tabs);
    ui_tabs_draw(r, &tabs, ui->app_mode, ui->mouse_x, ui->mouse_y);
}

void sound_editor_layout(const UiState *ui, SoundEditorLayout *lo) {
    int chrome = UI_APP_CHROME_H;
    int tab_w;
    int btn_gap = UI_UNIT;
    if (!lo) {
        return;
    }
    memset(lo, 0, sizeof(*lo));
    lo->content_y = chrome;
    /* Compact text-sized tabs, flush left (same edge as Graphics|Audio). */
    tab_w = font_text_width("Music");
    if (font_text_width("SFX") > tab_w) {
        tab_w = font_text_width("SFX");
    }
    tab_w += UI_UNIT;
    tab_w = ((tab_w + UI_UNIT - 1) / UI_UNIT) * UI_UNIT;
    if (tab_w < UI_UNIT) {
        tab_w = UI_UNIT;
    }
    lo->plane_tab_w = tab_w;
    lo->plane_tabs_x = 0;
    lo->plane_tabs_y = chrome;
    lo->track_list_y = chrome + UI_BTN_H + UI_UNIT;
    lo->track_row_h = UI_SPRITE_ROW_H; /* 16 */
    lo->add_w = ((label_width("Add") + UI_UNIT - 1) / UI_UNIT) * UI_UNIT;
    lo->add_x = UI_WORLDS_X + UI_UNIT;
    lo->add_y = ui_logic_h(ui) - UI_BTN_H - UI_UNIT;
    if (lo->add_y < lo->track_list_y + UI_BTN_H) {
        lo->add_y = lo->track_list_y + UI_BTN_H;
    }

    lo->lane_label_w = ((label_width("Pulse1") + UI_UNIT + UI_UNIT - 1) / UI_UNIT) * UI_UNIT;
    lo->lane_label_x = UI_SIDEBAR_W + UI_UNIT;
    lo->timeline_x = lo->lane_label_x + lo->lane_label_w;
    lo->hdr_y = chrome + UI_UNIT;
    lo->ruler_h = UI_BTN_H; /* 16 */
    lo->timeline_y = lo->hdr_y + UI_BTN_H + lo->ruler_h;
    lo->lane_h = UI_SOUND_LANE_H;
    lo->lane_gap = UI_SOUND_LANE_GAP;
    lo->px_per_tick = UI_SOUND_PX_PER_TICK;
    lo->timeline_h = UI_SOUND_BGM_CH * (lo->lane_h + lo->lane_gap) - lo->lane_gap;
    lo->minimap_h = UI_SOUND_MINIMAP_H;
    lo->minimap_y = lo->timeline_y + lo->timeline_h + UI_UNIT;
    {
        int max_w = ui_ctrl_x(ui) - UI_UNIT - lo->timeline_x;
        max_w = (max_w / UI_UNIT) * UI_UNIT;
        if (max_w < lo->px_per_tick * 4) {
            max_w = lo->px_per_tick * 4;
        }
        lo->timeline_w = max_w;
    }
    lo->visible_ticks = lo->timeline_w / lo->px_per_tick;
    if (lo->visible_ticks < 1) {
        lo->visible_ticks = 1;
    }

    lo->insp_x = ui_ctrl_x(ui) + UI_UNIT;
    lo->insp_y = chrome + UI_UNIT;
    lo->play_w = ((label_width("Play") + UI_UNIT - 1) / UI_UNIT) * UI_UNIT;
    lo->pause_w = ((label_width("Pause") + UI_UNIT - 1) / UI_UNIT) * UI_UNIT;
    lo->stop_w = ((label_width("Stop") + UI_UNIT - 1) / UI_UNIT) * UI_UNIT;
    lo->play_x = lo->insp_x;
    lo->play_y = lo->insp_y;
    lo->pause_x = lo->play_x + lo->play_w + btn_gap;
    lo->pause_y = lo->play_y;
    lo->stop_x = lo->pause_x + lo->pause_w + btn_gap;
    lo->stop_y = lo->play_y;
    /* Isolate radios: All on ruler row, channels centered on each lane. */
    lo->ch_radio_y0 = lo->timeline_y - lo->ruler_h;
}

void sound_plane_tabs_prepare(const UiState *ui, UiTabsLayout *out) {
    static const char *const labs[] = {"Music", "SFX"};
    SoundEditorLayout lo;
    sound_editor_layout(ui, &lo);
    if (!out) {
        return;
    }
    ui_tabs_layout(labs, 2, lo.plane_tabs_x, lo.plane_tabs_y, lo.plane_tab_w, out);
    out->tab_h = UI_BTN_H;
}

int sound_plane_tab_hit(const UiState *ui, int lx, int ly, int *out_idx) {
    UiTabsLayout tabs;
    sound_plane_tabs_prepare(ui, &tabs);
    return ui_tabs_hit(&tabs, ui ? ui->sound.plane : 0, lx, ly, out_idx);
}

int sound_track_hit(const UiState *ui, int lx, int ly, int *out_idx) {
    SoundEditorLayout lo;
    int i;
    int n;
    if (!ui) {
        return 0;
    }
    sound_editor_layout(ui, &lo);
    n = ui->sound.track_count;
    if (n < 0) {
        n = 0;
    }
    if (n > UI_SOUND_TRACKS_MAX) {
        n = UI_SOUND_TRACKS_MAX;
    }
    for (i = 0; i < n; i++) {
        int y = lo.track_list_y + i * lo.track_row_h;
        if (point_in_rect(lx, ly, 0, y, UI_SIDEBAR_W, lo.track_row_h)) {
            if (out_idx) {
                *out_idx = i;
            }
            return 1;
        }
    }
    return 0;
}

int sound_add_hit(const UiState *ui, int lx, int ly) {
    SoundEditorLayout lo;
    if (!ui) {
        return 0;
    }
    sound_editor_layout(ui, &lo);
    return point_in_rect(lx, ly, lo.add_x, lo.add_y, lo.add_w, UI_BTN_H);
}

int sound_timeline_hit(const UiState *ui, int lx, int ly, int *out_ch, int *out_tick) {
    SoundEditorLayout lo;
    int ch;
    int tick;
    if (!ui) {
        return 0;
    }
    sound_editor_layout(ui, &lo);
    if (!point_in_rect(lx, ly, lo.timeline_x, lo.timeline_y, lo.timeline_w, lo.timeline_h)) {
        return 0;
    }
    ch = (ly - lo.timeline_y) / (lo.lane_h + lo.lane_gap);
    if (ch < 0 || ch >= UI_SOUND_BGM_CH) {
        return 0;
    }
    tick = ui->sound.scroll_x + (lx - lo.timeline_x) / lo.px_per_tick;
    if (tick < 0) {
        tick = 0;
    }
    if (out_ch) {
        *out_ch = ch;
    }
    if (out_tick) {
        *out_tick = tick;
    }
    return 1;
}

int sound_region_hit(const UiState *ui, int lx, int ly, int *out_ch, int *out_region, int *out_handle) {
    SoundEditorLayout lo;
    int ch, i;
    int track;
    int vis0, vis1;
    if (!ui) {
        return 0;
    }
    sound_editor_layout(ui, &lo);
    if (!point_in_rect(lx, ly, lo.timeline_x, lo.timeline_y, lo.timeline_w, lo.timeline_h)) {
        return 0;
    }
    ch = (ly - lo.timeline_y) / (lo.lane_h + lo.lane_gap);
    if (ch < 0 || ch >= UI_SOUND_BGM_CH) {
        return 0;
    }
    track = ui->sound.track_idx;
    if (track < 0 || track >= ui->sound.track_count) {
        track = 0;
    }
    vis0 = ui->sound.scroll_x;
    vis1 = vis0 + lo.visible_ticks + 1;
    for (i = 0; i < ui->sound.region_count[track][ch]; i++) {
        const UiBgmRegion *rg = &ui->sound.region[track][ch][i];
        int x0, x1, y0, hw;
        int handle = 1;
        if (rg->start + rg->len <= vis0 || rg->start >= vis1) {
            continue;
        }
        x0 = lo.timeline_x + (rg->start - vis0) * lo.px_per_tick;
        x1 = lo.timeline_x + (rg->start + rg->len - vis0) * lo.px_per_tick;
        y0 = lo.timeline_y + ch * (lo.lane_h + lo.lane_gap);
        if (!point_in_rect(lx, ly, x0, y0, x1 - x0, lo.lane_h)) {
            continue;
        }
        hw = UI_SOUND_HANDLE_W;
        if (hw * 2 >= (x1 - x0)) {
            hw = (x1 - x0) / 3;
            if (hw < 1) {
                hw = 1;
            }
        }
        if (lx < x0 + hw) {
            handle = 2;
        } else if (lx >= x1 - hw) {
            handle = 3;
        }
        if (out_ch) {
            *out_ch = ch;
        }
        if (out_region) {
            *out_region = i;
        }
        if (out_handle) {
            *out_handle = handle;
        }
        return handle;
    }
    return 0;
}

int sound_channel_hit(const UiState *ui, int lx, int ly, int *out_ch) {
    /* Nano: no isolate radios (single Music lane). */
    (void)ui;
    (void)lx;
    (void)ly;
    (void)out_ch;
    return 0;
}

int sound_play_hit(const UiState *ui, int lx, int ly) {
    SoundEditorLayout lo;
    if (!ui) {
        return 0;
    }
    sound_editor_layout(ui, &lo);
    return point_in_rect(lx, ly, lo.play_x, lo.play_y, lo.play_w, UI_BTN_H);
}

int sound_pause_hit(const UiState *ui, int lx, int ly) {
    SoundEditorLayout lo;
    if (!ui) {
        return 0;
    }
    sound_editor_layout(ui, &lo);
    return point_in_rect(lx, ly, lo.pause_x, lo.pause_y, lo.pause_w, UI_BTN_H);
}

int sound_stop_hit(const UiState *ui, int lx, int ly) {
    SoundEditorLayout lo;
    if (!ui) {
        return 0;
    }
    sound_editor_layout(ui, &lo);
    return point_in_rect(lx, ly, lo.stop_x, lo.stop_y, lo.stop_w, UI_BTN_H);
}

static void ui_sound_add_demo_region(UiState *ui, int ch, int start, int len, const char *tok) {
    UiBgmRegion rg;
    memset(&rg, 0, sizeof(rg));
    rg.start = start;
    rg.len = len;
    snprintf(rg.tok, sizeof(rg.tok), "%s", tok);
    if (ch == 3) {
        int hex = 0;
        if (tok[0] == '8' && tok[1]) {
            char c = tok[1];
            if (c >= '0' && c <= '9') {
                hex = c - '0';
            } else if (c >= 'A' && c <= 'F') {
                hex = 10 + c - 'A';
            } else if (c >= 'a' && c <= 'f') {
                hex = 10 + c - 'a';
            }
        }
        rg.midi = hex;
    } else if (ch == 4) {
        rg.midi = 0xFD;
    } else {
        rg.midi = ui_bgm_tok_to_midi(tok);
        if (rg.midi < 0) {
            rg.midi = 60;
        }
    }
    (void)ui_bgm_place_region(ui, 0, ch, &rg);
}

void ui_sound_init(UiState *ui) {
    UiSoundEdit *s;
    if (!ui) {
        return;
    }
    s = &ui->sound;
    memset(s, 0, sizeof(*s));
    s->plane = UI_SOUND_PLANE_BGM;
    s->track_count = 2;
    s->track_idx = 0;
    s->solo_ch = UI_SOUND_SOLO_ALL;
    s->scroll_x = 0;
    s->sel_kind = UI_SOUND_SEL_NONE;
    s->playing = 0;
    s->paused = 0;
    s->play_pos = -1.f;
    snprintf(s->track_name[0], sizeof(s->track_name[0]), "Track 1");
    snprintf(s->track_name[1], sizeof(s->track_name[1]), "Track 2");
    /* Demo regions (quarter-note ticks), converted from former step grid. */
    ui_sound_add_demo_region(ui, 0, 0, 2, "C4");
    ui_sound_add_demo_region(ui, 0, 2, 2, "D4");
    ui_sound_add_demo_region(ui, 0, 4, 2, "E4");
    ui_sound_add_demo_region(ui, 0, 6, 1, "C4");
    ui_sound_add_demo_region(ui, 1, 0, 2, "E4");
    ui_sound_add_demo_region(ui, 1, 2, 2, "F4");
    ui_sound_add_demo_region(ui, 1, 4, 2, "G4");
    ui_sound_add_demo_region(ui, 1, 7, 1, "E4");
    ui_sound_add_demo_region(ui, 2, 0, 2, "G3");
    ui_sound_add_demo_region(ui, 2, 2, 2, "A3");
    ui_sound_add_demo_region(ui, 2, 4, 1, "B3");
    ui_sound_add_demo_region(ui, 2, 5, 1, "G3");
    ui_sound_add_demo_region(ui, 3, 1, 1, "8F");
    ui_sound_add_demo_region(ui, 3, 5, 1, "8F");
    ui_sound_add_demo_region(ui, 4, 2, 1, "FD");
}
