gustavostuff/GameNerd/app/sim/chips/atmega1284p.c

#include "atmega1284p.h"

#include "retr01_sim/bus.h"

#include <string.h>

static int port_is_data(const R01sEntity *e) {
    return r01s_level_is_high(r01s_entity_sense(e, "A0"));
}

static void mcu_reset(R01sEntity *e) {
    R01sAtmega1284p *c = (R01sAtmega1284p *)e;
    memset(c->oam, 0xFF, sizeof(c->oam)); /* unused slots: tile == 0xFF */
    memset(c->eeprom_mb, 0, sizeof(c->eeprom_mb));
    c->oam_addr = 0;
    c->soft_ppuctrl = 0;
    c->soft_raster_ctrl = 0;
    c->soft_bg0_x = 0;
    c->soft_bg0_y = 0;
    c->soft_pal_addr = 0;
    c->soft_map_lo = 0;
    c->soft_map_mid = 0;
    c->soft_map_hi = 0;
    c->soft_map_addr = 0;
    c->soft_cart_a14_18 = 0;
    c->soft_last_strobe = 0xFF;
    c->last_dq = 0;
    c->we_prev = 0;
    c->oe_prev = 0;
    c->clk_ticks = 0;
    c->alive = 0;
    r01s_bus_hiz(e, "DQ", 8);
}

static void mcu_eval(R01sEntity *e) {
    R01sAtmega1284p *c = (R01sAtmega1284p *)e;
    int ce = r01s_level_is_low(r01s_entity_sense(e, "CE#"));
    int oe = r01s_level_is_low(r01s_entity_sense(e, "OE#"));
    int we = r01s_level_is_low(r01s_entity_sense(e, "WE#"));
    int data = port_is_data(e);
    uint8_t v;

    if (!ce) {
        c->we_prev = 0;
        c->oe_prev = 0;
        r01s_bus_hiz(e, "DQ", 8);
        return;
    }

    /* Edge-trigger so settle-loop re-evals do not multi-inc OAM. */
    if (we && !c->we_prev) {
        v = (uint8_t)r01s_bus_read(e, "DQ", 8);
        if (data) {
            c->oam[c->oam_addr] = v;
            c->oam_addr = (uint16_t)((c->oam_addr + 1u) % R01S_OAM_BYTES);
        } else {
            /* $FE20: load bits [7:0], clear bit 8. Sequential $FE21 fill crosses into high half. */
            c->oam_addr = v;
        }
    }
    c->we_prev = we;

    if (oe && !c->oe_prev) {
        if (data) {
            c->last_dq = c->oam[c->oam_addr];
            c->oam_addr = (uint16_t)((c->oam_addr + 1u) % R01S_OAM_BYTES);
        } else {
            c->last_dq = (uint8_t)(c->oam_addr & 0xFFu);
        }
    }
    c->oe_prev = oe;

    if (we) {
        r01s_bus_hiz(e, "DQ", 8);
        return;
    }
    if (oe) {
        r01s_bus_write(e, "DQ", 8, c->last_dq);
        return;
    }
    r01s_bus_hiz(e, "DQ", 8);
}

static void mcu_tick(R01sEntity *e) {
    R01sAtmega1284p *c = (R01sAtmega1284p *)e;
    /* Sim-domain stub for 20 MHz -- full LCM master tick lands with N/K polish. */
    if (r01s_level_is_high(r01s_entity_sense(e, "CLK"))) {
        c->clk_ticks++;
        c->alive = 1;
    }
    r01s_entity_drive(e, "RUN", c->alive ? R01S_LVL_H : R01S_LVL_L);
}

static void mcu_destroy(R01sEntity *e) {
    (void)e;
}

static const R01sEntityVTable MCU1284_VT = {mcu_reset, mcu_eval, mcu_tick, mcu_destroy};

void r01s_atmega1284p_init(R01sAtmega1284p *chip, const char *refdes) {
    if (!chip) {
        return;
    }
    memset(chip, 0, sizeof(*chip));
    r01s_entity_init(&chip->base, &MCU1284_VT, "ATMEGA1284P", refdes ? refdes : "U1284");
    chip->base.impl = chip;

    /* Simplified OAM port (not full AVR PDIP map -- decode TBD on schematic). */
    r01s_entity_add_pin(&chip->base, 1, "RESET#", R01S_PIN_IN);
    r01s_entity_add_pin(&chip->base, 2, "CE#", R01S_PIN_IN);
    r01s_entity_add_pin(&chip->base, 3, "OE#", R01S_PIN_IN);
    r01s_entity_add_pin(&chip->base, 4, "WE#", R01S_PIN_IN);
    r01s_entity_add_pin(&chip->base, 5, "A0", R01S_PIN_IN);
    r01s_entity_add_pin(&chip->base, 6, "DQ0", R01S_PIN_IO);
    r01s_entity_add_pin(&chip->base, 7, "DQ1", R01S_PIN_IO);
    r01s_entity_add_pin(&chip->base, 8, "DQ2", R01S_PIN_IO);
    r01s_entity_add_pin(&chip->base, 9, "DQ3", R01S_PIN_IO);
    r01s_entity_add_pin(&chip->base, 10, "VCC", R01S_PIN_PWR);
    r01s_entity_add_pin(&chip->base, 11, "GND", R01S_PIN_PWR);
    r01s_entity_add_pin(&chip->base, 12, "DQ4", R01S_PIN_IO);
    r01s_entity_add_pin(&chip->base, 13, "DQ5", R01S_PIN_IO);
    r01s_entity_add_pin(&chip->base, 14, "DQ6", R01S_PIN_IO);
    r01s_entity_add_pin(&chip->base, 15, "DQ7", R01S_PIN_IO);
    r01s_entity_add_pin(&chip->base, 16, "CLK", R01S_PIN_IN);
    r01s_entity_add_pin(&chip->base, 17, "HBLANK", R01S_PIN_IN);
    r01s_entity_add_pin(&chip->base, 18, "RUN", R01S_PIN_OUT);
    r01s_entity_add_pin(&chip->base, 19, "NC", R01S_PIN_NC);
    r01s_entity_add_pin(&chip->base, 20, "NC", R01S_PIN_NC);
    r01s_entity_add_pin(&chip->base, 21, "NC", R01S_PIN_NC);
    r01s_entity_add_pin(&chip->base, 22, "NC", R01S_PIN_NC);
    r01s_entity_add_pin(&chip->base, 23, "NC", R01S_PIN_NC);
    r01s_entity_add_pin(&chip->base, 24, "NC", R01S_PIN_NC);
    r01s_entity_add_pin(&chip->base, 25, "NC", R01S_PIN_NC);
    r01s_entity_add_pin(&chip->base, 26, "NC", R01S_PIN_NC);
    r01s_entity_add_pin(&chip->base, 27, "NC", R01S_PIN_NC);
    r01s_entity_add_pin(&chip->base, 28, "NC", R01S_PIN_NC);
    r01s_entity_add_pin(&chip->base, 29, "NC", R01S_PIN_NC);
    r01s_entity_add_pin(&chip->base, 30, "NC", R01S_PIN_NC);
    r01s_entity_add_pin(&chip->base, 31, "NC", R01S_PIN_NC);
    r01s_entity_add_pin(&chip->base, 32, "NC", R01S_PIN_NC);
    r01s_entity_add_pin(&chip->base, 33, "NC", R01S_PIN_NC);
    r01s_entity_add_pin(&chip->base, 34, "NC", R01S_PIN_NC);
    r01s_entity_add_pin(&chip->base, 35, "NC", R01S_PIN_NC);
    r01s_entity_add_pin(&chip->base, 36, "NC", R01S_PIN_NC);
    r01s_entity_add_pin(&chip->base, 37, "NC", R01S_PIN_NC);
    r01s_entity_add_pin(&chip->base, 38, "NC", R01S_PIN_NC);
    r01s_entity_add_pin(&chip->base, 39, "NC", R01S_PIN_NC);
    r01s_entity_add_pin(&chip->base, 40, "AVCC", R01S_PIN_PWR);
    r01s_entity_set_dip_mm(&chip->base, 40, 53, 14);
    r01s_entity_reset(&chip->base);
}

R01sEntity *r01s_atmega1284p_entity(R01sAtmega1284p *chip) {
    return chip ? &chip->base : NULL;
}

uint16_t r01s_atmega1284p_oam_addr(const R01sAtmega1284p *chip) {
    return chip ? chip->oam_addr : 0;
}

uint8_t r01s_atmega1284p_oam_peek(const R01sAtmega1284p *chip, uint16_t addr) {
    if (!chip || addr >= R01S_OAM_BYTES) {
        return 0;
    }
    return chip->oam[addr];
}

void r01s_atmega1284p_oam_poke(R01sAtmega1284p *chip, uint16_t addr, uint8_t data) {
    if (chip && addr < R01S_OAM_BYTES) {
        chip->oam[addr] = data;
    }
}

uint8_t r01s_atmega1284p_eeprom_peek(const R01sAtmega1284p *chip, unsigned i) {
    if (!chip || i >= R01S_MCU1284_EEPROM_MAILBOX) {
        return 0;
    }
    return chip->eeprom_mb[i];
}

void r01s_atmega1284p_eeprom_poke(R01sAtmega1284p *chip, unsigned i, uint8_t data) {
    if (!chip || i >= R01S_MCU1284_EEPROM_MAILBOX) {
        return;
    }
    chip->eeprom_mb[i] = data;
}

static void soft_sync_map(R01sAtmega1284p *c) {
    c->soft_map_addr =
        ((uint32_t)c->soft_map_hi << 16) | ((uint32_t)c->soft_map_mid << 8) | c->soft_map_lo;
    c->soft_cart_a14_18 = (uint8_t)((c->soft_map_addr >> 14) & 0x1Fu);
}

int r01s_atmega1284p_soft_write(R01sAtmega1284p *chip, uint8_t port, uint8_t data) {
    if (!chip) {
        return 0;
    }
    switch (port) {
    case 0x00:
        chip->soft_ppuctrl = data;
        break;
    case 0x05:
        chip->soft_raster_ctrl = data;
        break;
    case 0x06:
        chip->soft_bg0_x = data;
        break;
    case 0x07:
        chip->soft_bg0_y = data;
        break;
    case 0x08:
        chip->soft_pal_addr = (uint8_t)(data & 0x1Fu);
        break;
    case 0x90:
        chip->soft_map_lo = data;
        soft_sync_map(chip);
        break;
    case 0x91:
        chip->soft_map_mid = data;
        soft_sync_map(chip);
        break;
    case 0x92:
        chip->soft_map_hi = data;
        soft_sync_map(chip);
        break;
    default:
        return 0;
    }
    chip->soft_last_strobe = port;
    return 1;
}

uint8_t r01s_atmega1284p_soft_read(const R01sAtmega1284p *chip, uint8_t port) {
    if (!chip) {
        return 0;
    }
    switch (port) {
    case 0x00:
        return chip->soft_ppuctrl;
    case 0x05:
        return chip->soft_raster_ctrl;
    case 0x06:
        return chip->soft_bg0_x;
    case 0x07:
        return chip->soft_bg0_y;
    case 0x08:
        return chip->soft_pal_addr;
    case 0x90:
        return chip->soft_map_lo;
    case 0x91:
        return chip->soft_map_mid;
    case 0x92:
        return chip->soft_map_hi;
    default:
        return 0;
    }
}

uint32_t r01s_atmega1284p_soft_map_addr(const R01sAtmega1284p *chip) {
    return chip ? chip->soft_map_addr : 0;
}

uint32_t r01s_atmega1284p_clk_ticks(const R01sAtmega1284p *chip) {
    return chip ? chip->clk_ticks : 0;
}

int r01s_atmega1284p_alive(const R01sAtmega1284p *chip) {
    return chip && chip->alive;
}
