gustavostuff/GameNerd/app/sim/tests/test_atmega1284p.c

#include "atmega1284p.h"
#include "retr01_sim/bus.h"
#include "test_common.h"

#include <stdio.h>

static void drive_a0(R01sEntity *e, int data_port) {
    r01s_entity_drive(e, "A0", data_port ? R01S_LVL_H : R01S_LVL_L);
}

static void write_port(R01sEntity *e, int data_port, uint8_t v) {
    drive_a0(e, data_port);
    r01s_entity_drive(e, "CE#", R01S_LVL_L);
    r01s_entity_drive(e, "OE#", R01S_LVL_H);
    r01s_entity_drive(e, "WE#", R01S_LVL_L);
    r01s_bus_write(e, "DQ", 8, v);
    r01s_entity_eval(e);
    r01s_entity_drive(e, "WE#", R01S_LVL_H);
    r01s_entity_eval(e);
    r01s_entity_drive(e, "CE#", R01S_LVL_H);
}

static uint8_t read_port(R01sEntity *e, int data_port) {
    uint8_t v;
    drive_a0(e, data_port);
    r01s_entity_drive(e, "CE#", R01S_LVL_L);
    r01s_entity_drive(e, "OE#", R01S_LVL_L);
    r01s_entity_drive(e, "WE#", R01S_LVL_H);
    r01s_entity_eval(e);
    v = (uint8_t)r01s_bus_read(e, "DQ", 8);
    r01s_entity_drive(e, "CE#", R01S_LVL_H);
    r01s_entity_drive(e, "OE#", R01S_LVL_H);
    r01s_entity_eval(e);
    return v;
}

int main(void) {
    R01sAtmega1284p chip;
    R01sEntity *e;
    int i;

    r01s_atmega1284p_init(&chip, "U1284");
    e = r01s_atmega1284p_entity(&chip);
    expect_true(e->dip_pins == 40, "40-pin package");

    write_port(e, 0, 0x00); /* $FE20 addr */
    write_port(e, 1, 0x10); /* Y */
    write_port(e, 1, 0x01); /* tile */
    write_port(e, 1, 0x00); /* attr */
    write_port(e, 1, 0x20); /* X */
    expect_true(r01s_atmega1284p_oam_peek(&chip, 0) == 0x10, "OAM Y");
    expect_true(r01s_atmega1284p_oam_peek(&chip, 1) == 0x01, "OAM tile");
    expect_true(r01s_atmega1284p_oam_peek(&chip, 3) == 0x20, "OAM X");
    expect_true(r01s_atmega1284p_oam_addr(&chip) == 4, "auto-inc to 4");

    write_port(e, 0, 0x00);
    expect_true(read_port(e, 1) == 0x10, "readback Y");
    expect_true(read_port(e, 1) == 0x01, "readback tile");
    expect_true(r01s_atmega1284p_oam_addr(&chip) == 2, "addr after 2 reads");

    r01s_entity_drive(e, "CLK", R01S_LVL_H);
    for (i = 0; i < 8; i++) {
        r01s_entity_tick(e);
    }
    expect_true(r01s_atmega1284p_clk_ticks(&chip) >= 8, "20 MHz domain ticks");
    expect_true(r01s_atmega1284p_alive(&chip), "alive");
    expect_true(r01s_entity_sense(e, "RUN") == R01S_LVL_H, "RUN high");

    r01s_atmega1284p_eeprom_poke(&chip, 0, 0xA5);
    expect_true(r01s_atmega1284p_eeprom_peek(&chip, 0) == 0xA5, "eeprom mailbox");

    expect_true(r01s_atmega1284p_soft_write(&chip, 0x08u, 0x15), "soft FE08 write");
    expect_true(r01s_atmega1284p_soft_read(&chip, 0x08u) == 0x15, "soft FE08 read");
    expect_true(r01s_atmega1284p_soft_write(&chip, 0x90u, 0x34), "soft FE90");
    expect_true(r01s_atmega1284p_soft_write(&chip, 0x91u, 0x12), "soft FE91");
    expect_true(r01s_atmega1284p_soft_write(&chip, 0x92u, 0x00), "soft FE92");
    expect_true(r01s_atmega1284p_soft_map_addr(&chip) == 0x001234u, "soft map_addr");
    expect_true(chip.soft_cart_a14_18 == (uint8_t)((0x001234u >> 14) & 0x1Fu), "cart A14-18");

    /* 128 OAM: sequential fill crosses into high half; ptr wraps at 512. */
    write_port(e, 0, 0x00);
    for (i = 0; i < 260; i++) {
        write_port(e, 1, (uint8_t)(i & 0xFF));
    }
    expect_true(r01s_atmega1284p_oam_addr(&chip) == 260, "auto-inc into high half");
    expect_true(r01s_atmega1284p_oam_peek(&chip, 256) == 0x00, "OAM[256] after wrap past 255");
    expect_true(r01s_atmega1284p_oam_peek(&chip, 259) == (uint8_t)(259 & 0xFF), "OAM[259]");
    r01s_atmega1284p_oam_poke(&chip, 400, 0x5A);
    expect_true(r01s_atmega1284p_oam_peek(&chip, 400) == 0x5A, "direct poke high OAM");

    return test_done("test_atmega1284p");
}
